ratatech/Talkbox/ltspice/talkbox.asc

C6: cap; 6.8nF
C8: cap; 10nF
C9: cap; 10µF
C10: cap; 10µF
C11: cap; 0.1µF
R13: res; {R_TONE}
R14: res; {R_TONE_SUB}
R15: res; 47k
R17: res; 22k
R18: res; {R_GAIN}
R19: res; {R_GAIN_SUB}
R20: res; 2k
R21: res; 1000k
U4: OP27
V2: voltage; 11.9
V3: voltage; 11.9
V4: voltage; SINE(0 0.15 1000); AC 1
Named nets: 0, Vcc, Vee, in
.options gmin=1e-9
.options abstol=1e-10
.options reltol=0.003
.options cshunt=1e-15
.option  ITL6=100
.ac oct 100 10 30K
.param R_TONE_SUB=10+{R_TONE_MAX}-{R_TONE}
.param R_TONE=8K
.step param R_TONE 10 20K 2K
.param R_GAIN=0.1
.param R_GAIN_SUB=20K-{R_GAIN}+10
;tran 0.010
;.step param R_GAIN 10 20000 2000
PARAMETERS
SIMULATION
.param R_VOL=5k
;.step param R_VOL 10 10000 500
.param R_VOL_SUB=10K-{R_VOL}+10
.param R_TONE_MAX=20K
.param R_TONE_STEP=0.1*{R_TONE_MAX}
